rolfwessels/switchscheduler/Photos/12vRelayBoard_bb.jpg

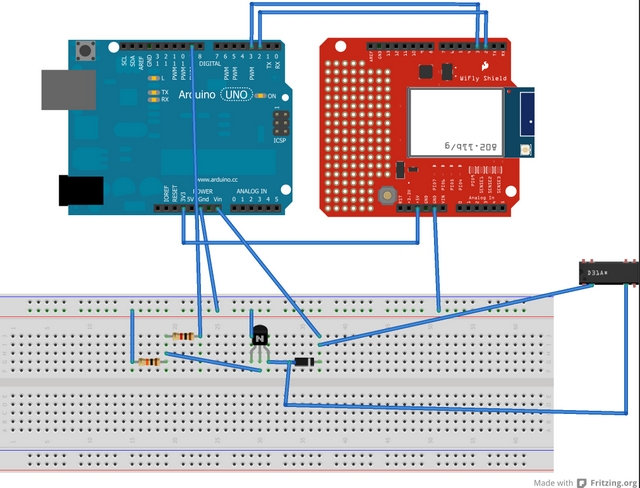
Photos/12vRelayBoard_bb.jpg
