rolfwessels/switchscheduler/Photos/boxview.png

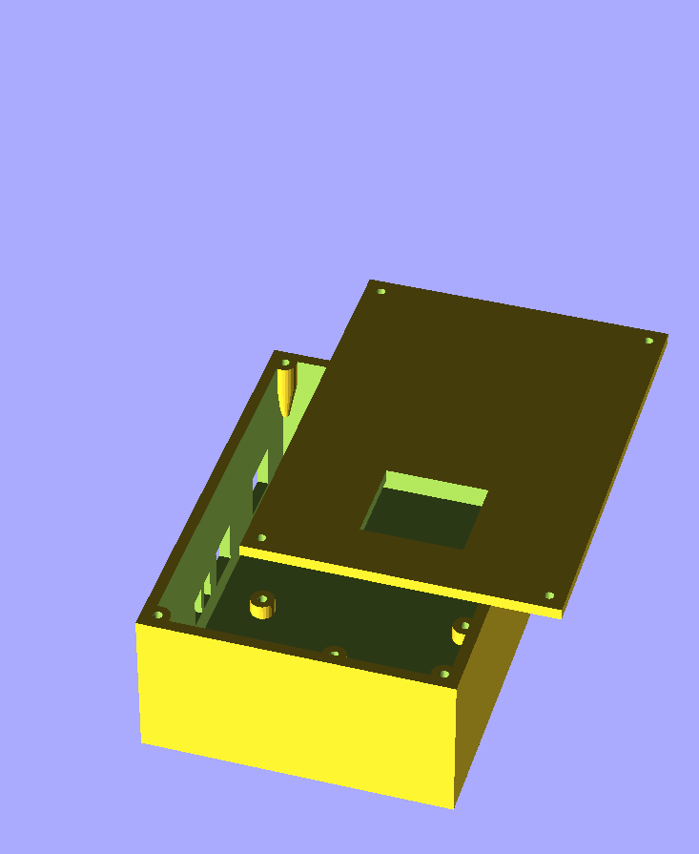
Photos/boxview.png
