rolfwessels/switchscheduler/Photos/Georg Lerm - this might help.jpg

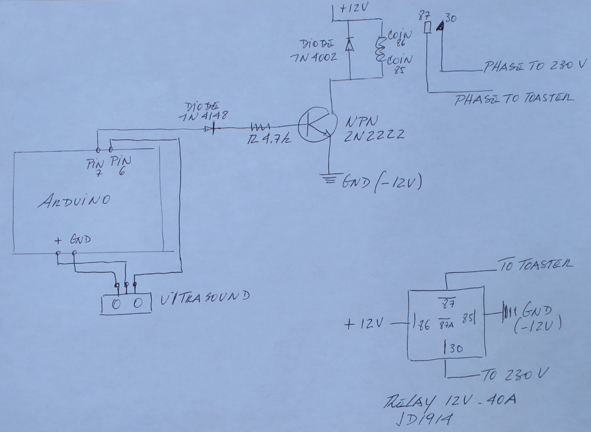
Photos/Georg Lerm - this might help.jpg
