rolfwessels/switchscheduler/Photos/image001.png

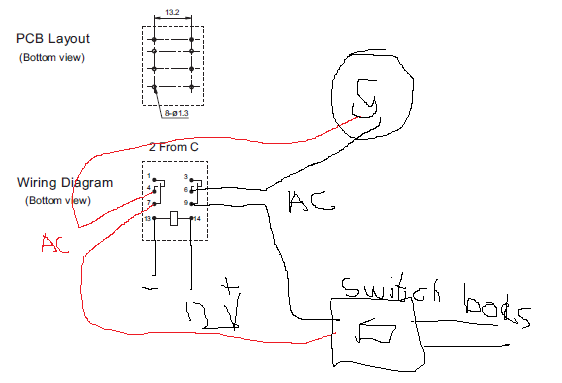
Photos/image001.png
