rolfwessels/switchscheduler/ArduinoRemoteSwitch/Credentials.h

#ifndef __CREDENTIALS_H__
#define __CREDENTIALS_H__

// Wifi parameters
char passphrase[] = "sogaanditmaar`";
char ssid[] = "FlyWi";
char ntp_server[] = "129.6.15.28"; // or your favorite ntp server.

#endif
